yaqwsx/MercuryXUpgrade/img/img2.jpg

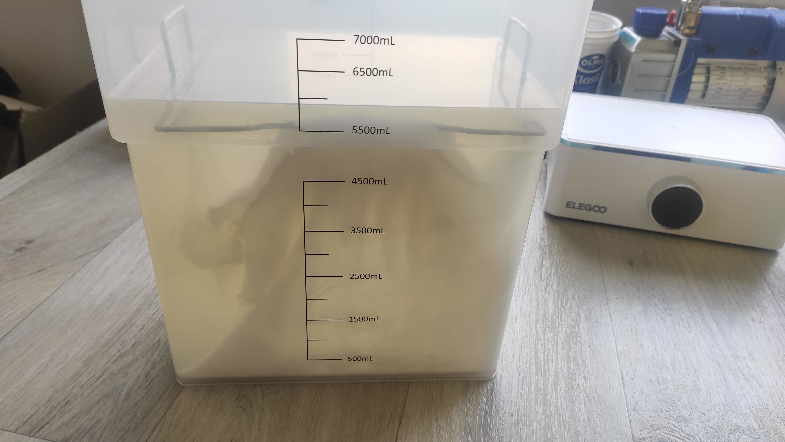
img/img2.jpg
