yaqwsx/MercuryXUpgrade/img/img11.jpg

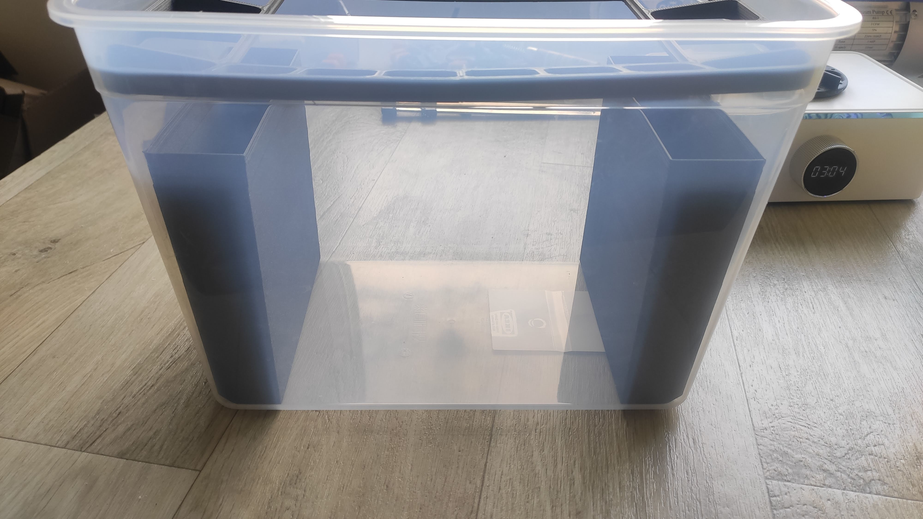
img/img11.jpg
