yaqwsx/MercuryXUpgrade/img/img12.jpg

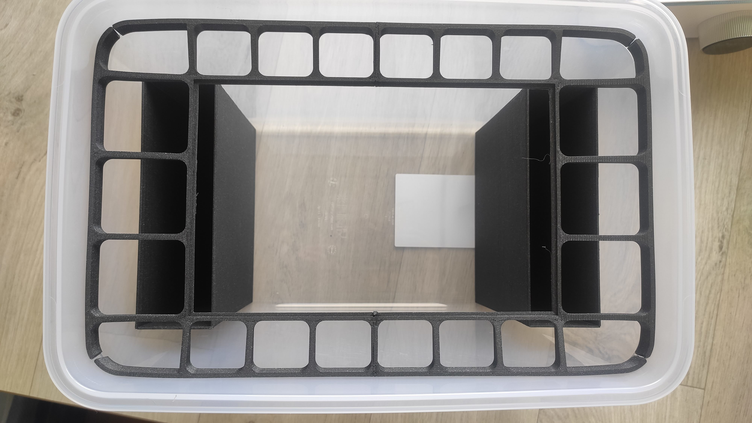
img/img12.jpg
