yaqwsx/MercuryXUpgrade/img/img16.jpg

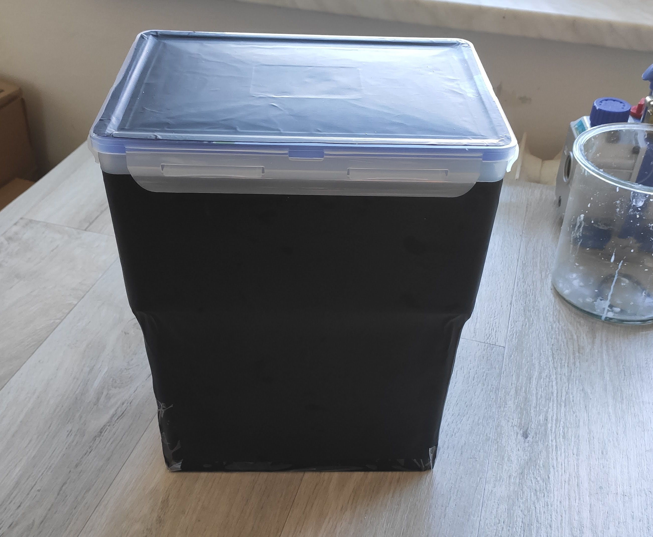
img/img16.jpg
