yaqwsx/MercuryXUpgrade/img/img17.jpg

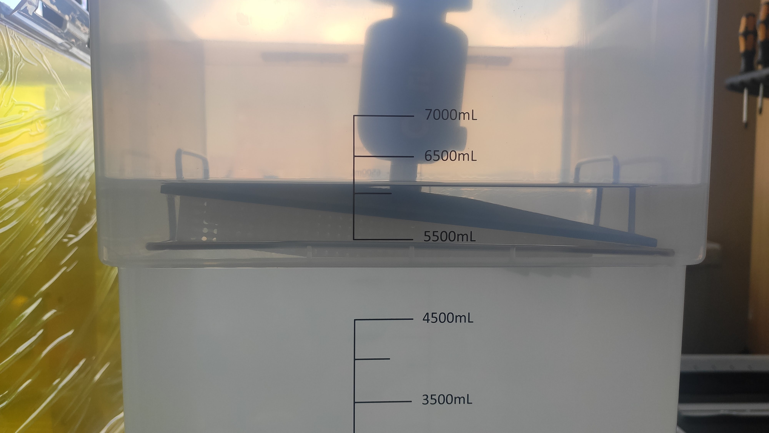
img/img17.jpg
